ZSWatch/Watch-DevKit-HW/cad/PCB-Holder/PCB-Holder v11.png

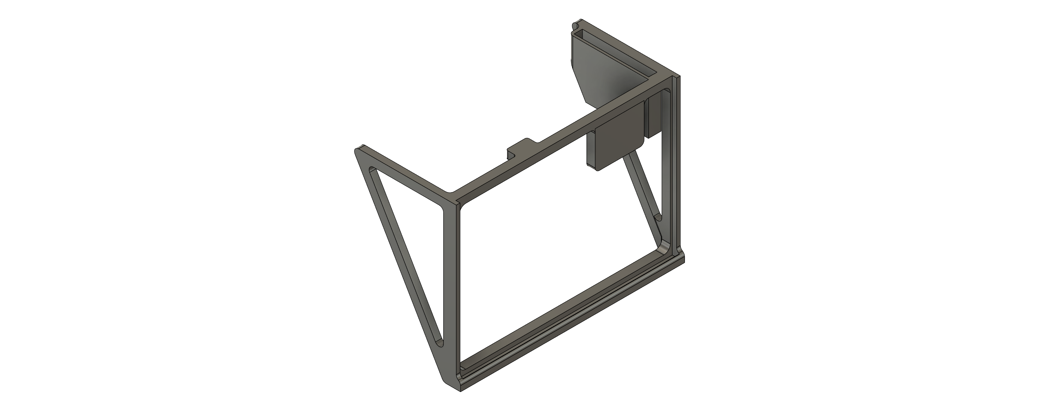
cad/PCB-Holder/PCB-Holder v11.png
