ZSWatch/Watch-DevKit-HW/production/watch-dk-PRELIMINARY/HTML/images/cat_png_3d_viewer_angled_top_ZSWatch-Watch-DevKit-angled_top.png

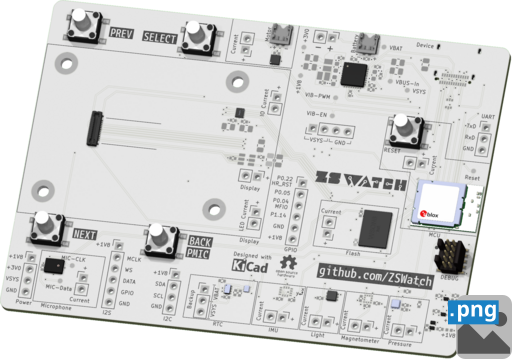
production/watch-dk-PRELIMINARY/HTML/images/cat_png_3d_viewer_angled_top_ZSWatch-Watch-DevKit-angled_top.png
