ZSWatch/Watch-DevKit-HW/production/watch-dk-PRELIMINARY/HTML/images/cat_png_3d_viewer_top_ZSWatch-Watch-DevKit-top.png

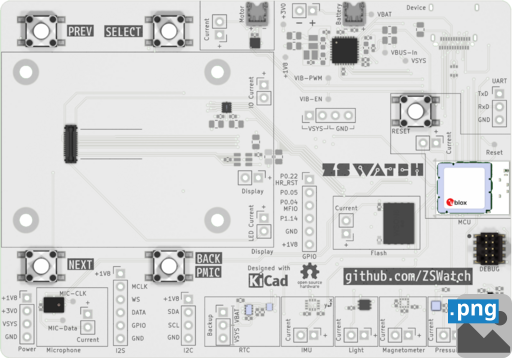
production/watch-dk-PRELIMINARY/HTML/images/cat_png_3d_viewer_top_ZSWatch-Watch-DevKit-top.png
