ZSWatch/Watch-DevKit-HW/production/watch-dk-PRELIMINARY/HTML/images/cat_pdf_assembly_ZSWatch-Watch-DevKit-assembly.png

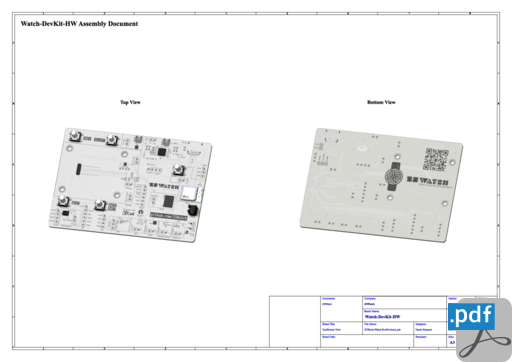
production/watch-dk-PRELIMINARY/HTML/images/cat_pdf_assembly_ZSWatch-Watch-DevKit-assembly.png
